jevans3142/adc-bar-lx/src/main/button_polling.c

// Button polling bits
//-----------------------------------

#include "freertos/FreeRTOS.h"
#include "driver/gpio.h"
#include "freertos/task.h"

#include "button_polling.h"
#include "redraw_screen.h"
#include "screen_driver.h"
#include "scene_engine.h"
#include "storage.c"

struct Scene_Engine_Settings_Struct Scene_Engine_Settings_temp;

static void special_msg_pop_task(void)
{
    vTaskDelay(SCREEN_MSG_POP_DURATION_MS);
    redraw_screen(get_screen());
    vTaskDelete(NULL);
}

static void menu_button_do(void)
{
    if (reset_display_active_status() == 1)
    {
        return;
    }

    switch (get_screen())
    {
    case SCREEN_MAIN_STATUS:
        if (get_lock_code() == 0)
        {
            set_screen(SCREEN_MAIN_MENU, 0);
        }
        else
        {
            set_screen_selected_value(1);
            set_screen(SCREEN_UNLOCK_CTRLS, 0);
        }
        break;
    case SCREEN_MAIN_MENU:
    case SCREEN_UNLOCK_CTRLS:
        set_screen(SCREEN_MAIN_STATUS, 0);
        break;

    case SCREEN_RECALL_SCENE:
    case SCREEN_RECORD_SCENE:
    case SCREEN_FADE_TIME:
    case SCREEN_S2L_MENU:
    case SCREEN_CF_MENU:
    case SCREEN_DMX_MODE:
    case SCREEN_LOCK_CTRLS:
    case SCREEN_ABOUT:
        set_screen(SCREEN_MAIN_MENU, get_screen() - 10);
        break;

    case SCREEN_S2L_MODE:
    case SCREEN_S2L_ENABLE:
    case SCREEN_S2L_H_CH:
    case SCREEN_S2L_MH_CH:
    case SCREEN_S2L_ML_CH:
    case SCREEN_S2L_L_CH:
        set_screen(SCREEN_S2L_MENU, get_screen() - 20);
        break;
    case SCREEN_RECORD_CONFIRM:
        set_screen(SCREEN_MAIN_MENU, SCREEN_RECORD_SCENE - 10);
        break;

    case SCREEN_CF_MODE: 
    case SCREEN_CF_ENABLE:
    case SCREEN_CF_TIME:
    case SCREEN_CF_R_CH:
    case SCREEN_CF_G_CH:
    case SCREEN_CF_B_CH:
        set_screen(SCREEN_CF_MENU, get_screen() - 30);
        break;
    }
}

static void set_button_do(void)
{
    if (reset_display_active_status() == 1)
    {
        return;
    }

    switch (get_screen())
    {
    case SCREEN_MAIN_STATUS:
        // No action
        break;
    case SCREEN_MAIN_MENU:
        // Going from main menu into subscreen
        switch (get_screen_selected_value() + 10)
        {
        case SCREEN_RECALL_SCENE:
            set_screen(SCREEN_RECALL_SCENE, 1);
            break;
        case SCREEN_RECORD_SCENE:
            set_screen(SCREEN_RECORD_SCENE, 1);
            break;
        case SCREEN_FADE_TIME:
            set_screen(SCREEN_FADE_TIME, get_scene_engine_settings().fade_time);
            break;
        case SCREEN_S2L_MENU:
            set_screen(SCREEN_S2L_MENU, 0);
            break;
        case SCREEN_CF_MENU:
            set_screen(SCREEN_CF_MENU, 0);
            break;        
        case SCREEN_DMX_MODE:
            set_screen(SCREEN_DMX_MODE, get_scene_engine_settings().dmx_input_mode);
            break;
        case SCREEN_LOCK_CTRLS:
            set_screen(SCREEN_LOCK_CTRLS, get_lock_code());
            break;
        case SCREEN_ABOUT:
            set_screen(SCREEN_ABOUT, 0);
            break;
        }

        break;

    case SCREEN_RECALL_SCENE:
        // Recall the selected scene
        set_scene(get_screen_selected_value());
        set_screen(SCREEN_MAIN_MENU, SCREEN_RECALL_SCENE - 10);
        break;
    case SCREEN_RECORD_SCENE:
        // Go to the record confirmation screen
        set_screen(SCREEN_RECORD_CONFIRM, get_screen_selected_value());
        break;
    case SCREEN_FADE_TIME:
        // Set the fade time
        Scene_Engine_Settings_temp = get_scene_engine_settings();
        Scene_Engine_Settings_temp.fade_time = get_screen_selected_value();
        set_scene_engine_settings(Scene_Engine_Settings_temp);
        set_screen(SCREEN_MAIN_MENU, SCREEN_FADE_TIME - 10);
        break;

    case SCREEN_S2L_MENU:
        // Going from sound to light menu into subscreen
        switch (get_screen_selected_value() + 20)
        {
        case SCREEN_S2L_MODE:
            set_screen(SCREEN_S2L_MODE, get_scene_engine_settings().s2l_mode);
            break;
        case SCREEN_S2L_ENABLE:
            set_screen(SCREEN_S2L_ENABLE, 1);
            break;
        case SCREEN_S2L_H_CH:
            set_screen(SCREEN_S2L_H_CH, get_scene_engine_settings().s2l_high_ch);
            break;
        case SCREEN_S2L_MH_CH:
            set_screen(SCREEN_S2L_MH_CH, get_scene_engine_settings().s2l_midhigh_ch);
            break;
        case SCREEN_S2L_ML_CH:
            set_screen(SCREEN_S2L_ML_CH, get_scene_engine_settings().s2l_midlow_ch);
            break;
        case SCREEN_S2L_L_CH:
            set_screen(SCREEN_S2L_L_CH, get_scene_engine_settings().s2l_low_ch);
            break;
        }
        break;

    case SCREEN_CF_MENU:
        // Going from colourfade menu into subscreen
        switch (get_screen_selected_value() + 30) 
        {
        case SCREEN_CF_MODE:
            set_screen(SCREEN_CF_MODE, get_scene_engine_settings().colourfade_mode);
            break;
        case SCREEN_CF_ENABLE:
            set_screen(SCREEN_CF_ENABLE, 1);
            break;
        case SCREEN_CF_TIME:
            set_screen(SCREEN_CF_TIME, get_scene_engine_settings().colourfade_time);
            break;
        case SCREEN_CF_R_CH:
            set_screen(SCREEN_CF_R_CH, get_scene_engine_settings().colourfade_r_ch);
            break;
        case SCREEN_CF_G_CH:
            set_screen(SCREEN_CF_G_CH, get_scene_engine_settings().colourfade_g_ch);
            break;
        case SCREEN_CF_B_CH:
            set_screen(SCREEN_CF_B_CH, get_scene_engine_settings().colourfade_b_ch);
            break;
        }
        break;

    case SCREEN_DMX_MODE:
        // Set the DMX mode
        Scene_Engine_Settings_temp = get_scene_engine_settings();
        Scene_Engine_Settings_temp.dmx_input_mode = get_screen_selected_value();
        set_scene_engine_settings(Scene_Engine_Settings_temp);
        set_screen(SCREEN_MAIN_MENU, SCREEN_DMX_MODE - 10);
        break;
    case SCREEN_LOCK_CTRLS:
        // Set the lock code and lock the display
        set_lock_code(get_screen_selected_value());
        set_screen(SCREEN_MAIN_STATUS, 0);
        break;
    case SCREEN_ABOUT:
        // No action
        break;

    case SCREEN_S2L_MODE:
        // Set the sound to light mode
        Scene_Engine_Settings_temp = get_scene_engine_settings();
        Scene_Engine_Settings_temp.s2l_mode = get_screen_selected_value();
        set_scene_engine_settings(Scene_Engine_Settings_temp);
        set_screen(SCREEN_S2L_MENU, SCREEN_S2L_MODE - 20);
        break;
    case SCREEN_S2L_ENABLE:
        // Toggle sound to light enable on the currently selected scene
        Scene_Engine_Settings_temp = get_scene_engine_settings();
        Scene_Engine_Settings_temp.s2l_enable[get_screen_selected_value() - 1] ^= 1;
        set_scene_engine_settings(Scene_Engine_Settings_temp);
        redraw_screen(get_screen());
        break;
    case SCREEN_S2L_H_CH:
        // Set the sound to light high channel
        Scene_Engine_Settings_temp = get_scene_engine_settings();
        Scene_Engine_Settings_temp.s2l_high_ch = get_screen_selected_value();
        set_scene_engine_settings(Scene_Engine_Settings_temp);
        set_screen(SCREEN_S2L_MENU, SCREEN_S2L_H_CH - 20);
        break;
    case SCREEN_S2L_MH_CH:
        // Set the sound to light mid high channel
        Scene_Engine_Settings_temp = get_scene_engine_settings();
        Scene_Engine_Settings_temp.s2l_midhigh_ch = get_screen_selected_value();
        set_scene_engine_settings(Scene_Engine_Settings_temp);
        set_screen(SCREEN_S2L_MENU, SCREEN_S2L_MH_CH - 20);
        break;
    case SCREEN_S2L_ML_CH:
        // Set the sound to light mid low channel
        Scene_Engine_Settings_temp = get_scene_engine_settings();
        Scene_Engine_Settings_temp.s2l_midlow_ch = get_screen_selected_value();
        set_scene_engine_settings(Scene_Engine_Settings_temp);
        set_screen(SCREEN_S2L_MENU, SCREEN_S2L_ML_CH - 20);
        break;
    case SCREEN_S2L_L_CH:
        // Set the sound to light low channel
        Scene_Engine_Settings_temp = get_scene_engine_settings();
        Scene_Engine_Settings_temp.s2l_low_ch = get_screen_selected_value();
        set_scene_engine_settings(Scene_Engine_Settings_temp);
        set_screen(SCREEN_S2L_MENU, SCREEN_S2L_L_CH - 20);
        break;

    case SCREEN_CF_MODE: 
        // Set the colourfade mode
        Scene_Engine_Settings_temp = get_scene_engine_settings();
        Scene_Engine_Settings_temp.colourfade_mode = get_screen_selected_value();
        set_scene_engine_settings(Scene_Engine_Settings_temp);
        set_screen(SCREEN_CF_MENU, SCREEN_CF_MODE - 30);
        break; 
    case SCREEN_CF_ENABLE:
        //  Toggle colourfade enable on the currently selected scene
        Scene_Engine_Settings_temp = get_scene_engine_settings();
        Scene_Engine_Settings_temp.colourfade_enable[get_screen_selected_value() - 1] ^= 1;
        set_scene_engine_settings(Scene_Engine_Settings_temp);
        redraw_screen(get_screen());
        break;
    case SCREEN_CF_TIME:
        // Set the colourfade time
        Scene_Engine_Settings_temp = get_scene_engine_settings();
        Scene_Engine_Settings_temp.colourfade_time = get_screen_selected_value();
        set_scene_engine_settings(Scene_Engine_Settings_temp);
        set_screen(SCREEN_CF_MENU, SCREEN_CF_TIME - 30);
        break;
    case SCREEN_CF_R_CH:
        // Set the colourfade red channel
        Scene_Engine_Settings_temp = get_scene_engine_settings();
        Scene_Engine_Settings_temp.colourfade_r_ch = get_screen_selected_value();
        set_scene_engine_settings(Scene_Engine_Settings_temp);
        set_screen(SCREEN_CF_MENU, SCREEN_CF_R_CH - 30);
        break;
    case SCREEN_CF_G_CH:
        // Set the colourfade green channel
        Scene_Engine_Settings_temp = get_scene_engine_settings();
        Scene_Engine_Settings_temp.colourfade_g_ch = get_screen_selected_value();
        set_scene_engine_settings(Scene_Engine_Settings_temp);
        set_screen(SCREEN_CF_MENU, SCREEN_CF_G_CH - 30);
        break;
    case SCREEN_CF_B_CH:
        // Set the colourfade blue channel
        Scene_Engine_Settings_temp = get_scene_engine_settings();
        Scene_Engine_Settings_temp.colourfade_b_ch = get_screen_selected_value();
        set_scene_engine_settings(Scene_Engine_Settings_temp);
        set_screen(SCREEN_CF_MENU, SCREEN_CF_B_CH - 30);
        break;

    case SCREEN_RECORD_CONFIRM:
        // Record the current DMX input to the selected scene
        record_scene(get_screen_selected_value());
        set_screen(SCREEN_MAIN_MENU, SCREEN_RECORD_SCENE - 10);
        break;

    case SCREEN_UNLOCK_CTRLS:
        // Determine if the unlock code is correct
        if (get_screen_selected_value() == get_lock_code())
        {
            // Yes - unlock the display
            set_lock_code(0);
            set_screen(SCREEN_MAIN_MENU, 0);
        }
        else
        {
            // No - display an X for a few seconds
            draw_string(70, 32, "X", DOUBLE_SIZE, WHITE);
            refresh_display();
            xTaskCreate((TaskFunction_t)special_msg_pop_task, "special_msg_pop_task", 2048, NULL, 5, NULL);
        }
        break;
    }
}

static void up_button_do(void)
{
    if (reset_display_active_status() == 1)
    {
        return;
    }

    switch (get_screen())
    {
    case SCREEN_MAIN_STATUS:
        // No action
        break;
    case SCREEN_RECORD_CONFIRM:
        // No action
        break;
    case SCREEN_MAIN_MENU:
        set_screen_selected_value_dec(7, 0);
        redraw_screen(get_screen());
        break;
    case SCREEN_RECALL_SCENE:
        set_screen_selected_value_inc(7, 1);
        redraw_screen(get_screen());
        break;
    case SCREEN_RECORD_SCENE:
        set_screen_selected_value_inc(7, 1);
        redraw_screen(get_screen());
        break;
    case SCREEN_FADE_TIME:
        set_screen_selected_value_inc(59, 1);
        redraw_screen(get_screen());
        break;
    case SCREEN_S2L_MENU:
        set_screen_selected_value_dec(5, 0);
        redraw_screen(get_screen());
        break;
    case SCREEN_CF_MENU:
        set_screen_selected_value_dec(5, 0);
        redraw_screen(get_screen());
        break;
    case SCREEN_DMX_MODE:
        set_screen_selected_value_inc(1, 0);
        redraw_screen(get_screen());
        break;
    case SCREEN_LOCK_CTRLS:
    case SCREEN_UNLOCK_CTRLS:
        set_screen_selected_value_inc(999, 1);
        redraw_screen(get_screen());
        break;
    case SCREEN_ABOUT:
        set_screen_selected_value_inc(1, 0);
        redraw_screen(get_screen());
        break;
    case SCREEN_S2L_MODE:
        set_screen_selected_value_inc(1, 0);
        redraw_screen(get_screen());
        break;
    case SCREEN_S2L_ENABLE:
        set_screen_selected_value_inc(7, 1);
        redraw_screen(get_screen());
        break;
    case SCREEN_S2L_H_CH:
    case SCREEN_S2L_MH_CH:
    case SCREEN_S2L_ML_CH:
    case SCREEN_S2L_L_CH:
        set_screen_selected_value_inc(512, 1);
        redraw_screen(get_screen());
        break;
    case SCREEN_CF_MODE: 
        set_screen_selected_value_inc(1, 0);
        redraw_screen(get_screen());
        break; 
    case SCREEN_CF_ENABLE:
        set_screen_selected_value_inc(7, 1);
        redraw_screen(get_screen());
        break;
    case SCREEN_CF_TIME:
        set_screen_selected_value_inc(59, 1);
        redraw_screen(get_screen());
        break;
    case SCREEN_CF_R_CH:
    case SCREEN_CF_G_CH:
    case SCREEN_CF_B_CH:
        set_screen_selected_value_inc(512, 1);
        redraw_screen(get_screen());
        break;
    }
}

static void down_button_do(void)
{
    if (reset_display_active_status() == 1)
    {
        return;
    }

    switch (get_screen())
    {
    case SCREEN_MAIN_STATUS:
        // No action
        break;
    case SCREEN_RECORD_CONFIRM:
        // No action
        break;
    case SCREEN_MAIN_MENU:
        set_screen_selected_value_inc(7, 0); // TODO: Replace magic numbers
        redraw_screen(get_screen());
        break;
    case SCREEN_RECALL_SCENE:
        set_screen_selected_value_dec(7, 1);
        redraw_screen(get_screen());
        break;
    case SCREEN_RECORD_SCENE:
        set_screen_selected_value_dec(7, 1);
        redraw_screen(get_screen());
        break;
    case SCREEN_FADE_TIME:
        set_screen_selected_value_dec(59, 1);
        redraw_screen(get_screen());
        break;
    case SCREEN_S2L_MENU:
        set_screen_selected_value_inc(5, 0);
        redraw_screen(get_screen());
        break;
    case SCREEN_CF_MENU:
        set_screen_selected_value_inc(5, 0);
        redraw_screen(get_screen());
        break;
    case SCREEN_DMX_MODE:
        set_screen_selected_value_dec(1, 0);
        redraw_screen(get_screen());
        break;
    case SCREEN_LOCK_CTRLS:
    case SCREEN_UNLOCK_CTRLS:
        set_screen_selected_value_dec(999, 1);
        redraw_screen(get_screen());
        break;
    case SCREEN_ABOUT:
        set_screen_selected_value_dec(1, 0);
        redraw_screen(get_screen());
        break;
    case SCREEN_S2L_MODE:
        set_screen_selected_value_dec(1, 0);
        redraw_screen(get_screen());
        break;
    case SCREEN_S2L_ENABLE:
        set_screen_selected_value_dec(7, 1);
        redraw_screen(get_screen());
        break;
    case SCREEN_S2L_H_CH:
    case SCREEN_S2L_MH_CH:
    case SCREEN_S2L_ML_CH:
    case SCREEN_S2L_L_CH:
        set_screen_selected_value_dec(512, 1);
        redraw_screen(get_screen());
        break;
    case SCREEN_CF_MODE: 
        set_screen_selected_value_dec(1, 0);
        redraw_screen(get_screen());
        break; 
    case SCREEN_CF_ENABLE:
        set_screen_selected_value_dec(7, 1);
        redraw_screen(get_screen());
        break;
    case SCREEN_CF_TIME:
        set_screen_selected_value_dec(59, 1);
        redraw_screen(get_screen());
        break;
    case SCREEN_CF_R_CH:
    case SCREEN_CF_G_CH:
    case SCREEN_CF_B_CH:
        set_screen_selected_value_dec(512, 1);
        redraw_screen(get_screen());
        break;
    }
}

static void special_flash_task(void)
{
    for (int i = 0; i < 6; i++)
    {
        gpio_set_level(PIN_SCENE_LEDS_BIT_1, 0);
        gpio_set_level(PIN_SCENE_LEDS_BIT_2, 0);
        gpio_set_level(PIN_SCENE_LEDS_BIT_4, 0);
        vTaskDelay(BUTTON_FLASH_INTERVAL_MS);
        gpio_set_level(PIN_SCENE_LEDS_BIT_1, 0);
        gpio_set_level(PIN_SCENE_LEDS_BIT_2, 1);
        gpio_set_level(PIN_SCENE_LEDS_BIT_4, 1);
        vTaskDelay(BUTTON_FLASH_INTERVAL_MS);
    }
    int scene_no = get_scene();
    gpio_set_level(PIN_SCENE_LEDS_BIT_1, (scene_no & 1));
    gpio_set_level(PIN_SCENE_LEDS_BIT_2, (scene_no & 2));
    gpio_set_level(PIN_SCENE_LEDS_BIT_4, (scene_no & 4));
    vTaskDelete(NULL);
}

static int scene_button_decode(void)
{
    return ((1 * !gpio_get_level(PIN_SCENE_BUTTONS_BIT_1)) + (2 * !gpio_get_level(PIN_SCENE_BUTTONS_BIT_2)) + (4 * !gpio_get_level(PIN_SCENE_BUTTONS_BIT_4)));
}

static void button_debounce(int button_pin, int *state, int *counter, void (*button_do)())
{
    if (gpio_get_level(button_pin))
    {
        *counter = 0;
        if (*state != 0)
        {
            *state = 0;
            button_do();
        }
    }
    else
    {
        *counter = *counter + 1;
    }
    if (*counter >= BUTTON_DEBOUNCE_TICKS)
    {
        *state = 1;
    }
}

void button_poll_task(void)
{
    gpio_config_t io_conf;
    io_conf.intr_type = GPIO_INTR_DISABLE;
    io_conf.mode = GPIO_MODE_INPUT;
    io_conf.pin_bit_mask = PIN_MENU_BUTTONS_MASK;
    io_conf.pull_down_en = GPIO_PULLDOWN_DISABLE;
    io_conf.pull_up_en = GPIO_PULLUP_ENABLE;
    gpio_config(&io_conf);

    io_conf.pin_bit_mask = PIN_SCENE_BUTTONS_MASK;
    gpio_config(&io_conf);

    int menu_counter = 0;
    int set_counter = 0;
    int up_counter = 0;
    int down_counter = 0;
    int scene_counter = 0;

    int menu_state = 0;
    int set_state = 0;
    int up_state = 0;
    int down_state = 0;
    int scene_state = 0;

    int scene_number = 0;

    while (1)
    {
        button_debounce(PIN_MENU_BUTTON, &menu_state, &menu_counter, menu_button_do);
        button_debounce(PIN_SET_BUTTON, &set_state, &set_counter, set_button_do);
        button_debounce(PIN_UP_BUTTON, &up_state, &up_counter, up_button_do);
        button_debounce(PIN_DOWN_BUTTON, &down_state, &down_counter, down_button_do);

        // Scene buttons
        int current_button_selected = scene_button_decode();
        if (current_button_selected == 0)
        {
            if (scene_state != 0)
            {
                // First check if this is the special record function
                if (scene_number == 6 && scene_counter > 500)
                {
                    // Record special scene
                    scene_state = 0;
                    record_scene(6);
                    xTaskCreate((TaskFunction_t)special_flash_task, "special_flash_task", 2048, NULL, 5, NULL);
                }
                else
                {
                    scene_state = 0;
                    set_scene(scene_number);
                    if (get_screen() == 0)
                    {
                        redraw_screen(0);
                    }
                }
            }
            scene_counter = 0;
            scene_number = 0;
        }
        else
        {
            if (current_button_selected == scene_number)
            {
                scene_counter++;
            }
            else
            {
                scene_counter = 0;
                scene_number = current_button_selected;
            }
        }
        if (scene_counter >= BUTTON_DEBOUNCE_TICKS)
        {
            scene_state = 1;
        }

        vTaskDelay(BUTTON_POLL_INTERVAL_MS);
    }
}
