jevans3142/adc-bar-lx/src/main/storage.h

// Storage module
//-----------------------------------

#ifndef STORAGE_H_INCLUDED
#define STORAGE_H_INCLUDED

//Pin defs
#define PIN_SD_MISO 19
#define PIN_SD_MOSI 23 
#define PIN_SD_CLK  18
#define PIN_SD_CS   5 
void init_sd_spi(void);
void write_scene(uint8_t scene_number, uint8_t* scene_data);
uint8_t read_scene(uint8_t scene_number, uint8_t* scene_data);
void write_settings(struct Scene_Engine_Settings_Struct input);
struct Scene_Engine_Settings_Struct read_settings(void);

#endif  
